RSDuck/nileswan/firmware/src/spi_cmd.c

/**
 * Copyright (c) 2024 Adrian Siekierka
 *
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
 * You should have received a copy of the GNU General Public License along
 * with Nileswan MCU. If not, see <https://www.gnu.org/licenses/>.
 */

#include <stdbool.h>
#include <stddef.h>
#include <stdint.h>
#include <string.h>

#include "class/cdc/cdc_device.h"
#include "config.h"
#include "mcu.h"
#include "cdc.h"
#include "nvram.h"
#include "spi_cmd.h"
#include "eeprom.h"
#include "rtc.h"
#include "tusb.h"

uint16_t spi_cmd;
#define SPI_NATIVE_CMD(n) ((n) & 0x7F)
#define SPI_NATIVE_ARG(n) ((n) >> 7)

static inline int arg_to_len(uint16_t arg) {
    return arg ? arg : 512;
}

int spi_native_start_command_rx(uint16_t cmd) {
    spi_cmd = cmd;
    uint16_t arg = SPI_NATIVE_ARG(spi_cmd);
    switch (SPI_NATIVE_CMD(spi_cmd)) {
    case MCU_SPI_CMD_ECHO:
    case MCU_SPI_CMD_USB_CDC_WRITE:
        return arg_to_len(arg);
    case MCU_SPI_CMD_EEPROM_WRITE:
        return (arg_to_len(arg) << 1) + 2;
    case MCU_SPI_CMD_EEPROM_READ:
        return 2;
    case MCU_SPI_CMD_SET_SAVE_ID:
        return 4;
    case MCU_SPI_CMD_RTC_COMMAND:
        return rtc_start_command_rx(arg);
    default:
        return 0;
    }
}

int spi_native_finish_command_rx(uint8_t *rx, uint8_t *tx) {
    uint16_t arg = SPI_NATIVE_ARG(spi_cmd);
#ifdef CONFIG_DEBUG_SPI_NATIVE_CMD
    cdc_debug("spi/native: received command %02X %04X", SPI_NATIVE_CMD(spi_cmd), arg);
#endif
    switch (SPI_NATIVE_CMD(spi_cmd)) {
    case MCU_SPI_CMD_ECHO:
        memcpy(tx, rx, arg_to_len(arg));
        return arg_to_len(arg);
    case MCU_SPI_CMD_MODE:
        if (arg == 0xFF) {
            mcu_shutdown();
        } else {
            mcu_spi_init(arg);
        }
        return -1;
    case MCU_SPI_CMD_FREQ:
        mcu_spi_set_freq(arg);
        tx[0] = 1;
        return 1;
    case MCU_SPI_CMD_ID:
        memcpy(tx, (void*) UID_BASE, MCU_UID_LENGTH);
        return MCU_UID_LENGTH;
    case MCU_SPI_CMD_EEPROM_MODE:
        eeprom_set_type(arg);
        tx[0] = 1;
        return 1;
    case MCU_SPI_CMD_EEPROM_ERASE:
        eeprom_erase();
        return 0;
    case MCU_SPI_CMD_EEPROM_WRITE:
        eeprom_write_data(rx + 2, *((uint16_t*) rx), arg_to_len(arg) << 1);
        return 0;
    case MCU_SPI_CMD_EEPROM_READ:
        eeprom_read_data(tx, *((uint16_t*) rx), arg_to_len(arg) << 1);
        return arg_to_len(arg) << 1;
    case MCU_SPI_CMD_RTC_COMMAND:
        return rtc_finish_command_rx(rx, tx);
    case MCU_SPI_CMD_EEPROM_GET_MODE:
        tx[0] = eeprom_get_type();
        return 1;
    case MCU_SPI_CMD_SET_SAVE_ID: {
        uint32_t save_id;
        memcpy(&save_id, rx, 4);
        if (arg & 0x1) nvram.save_id = save_id;
        else           nvram.save_id = SAVE_ID_NONE;
        if (arg & 0x2) TAMP->BKP8R = save_id;
        else           TAMP->BKP8R = SAVE_ID_NONE;
        tx[0] = 1;
    } return 1;
    case MCU_SPI_CMD_GET_SAVE_ID: {
        uint32_t save_id = SAVE_ID_NONE;
        if ((arg & 0x2) && TAMP->BKP8R   != SAVE_ID_NONE) save_id = TAMP->BKP8R;
        if ((arg & 0x1) && nvram.save_id != SAVE_ID_NONE) save_id = nvram.save_id;
        memcpy(tx, &save_id, 4);
    } return 4;
    case MCU_SPI_CMD_USB_CDC_READ:
        if (!tud_cdc_connected()) {
            return 0;
        }
        return tud_cdc_read(tx, arg_to_len(arg));
    case MCU_SPI_CMD_USB_CDC_WRITE: {
        if (!tud_cdc_connected()) {
            *((uint16_t*) tx) = 0;
        } else {
            *((uint16_t*) tx) = tud_cdc_write(rx, arg_to_len(arg));
            tud_cdc_write_flush();
        }
        return 2;
    }
    case MCU_SPI_CMD_USB_CDC_AVAILABLE: {
        if (!tud_cdc_connected()) {
            *((uint16_t*) tx) = 0;
        } else {
            *((uint16_t*) tx) = tud_cdc_available();
        }
        return 2;
    }
    default:
        return 0;
    }
}

#if 0
void tud_cdc_rx_cb(uint8_t itf) {
    if (itf == 0 && tud_cdc_n_available(itf)) {
        cdc_debug("available: %d\n", tud_cdc_n_available(itf));
    }
}
#endif
